sjlongland/dcdcconv-sensor-pcb/gerber/sensor-In2.Cu.pdf

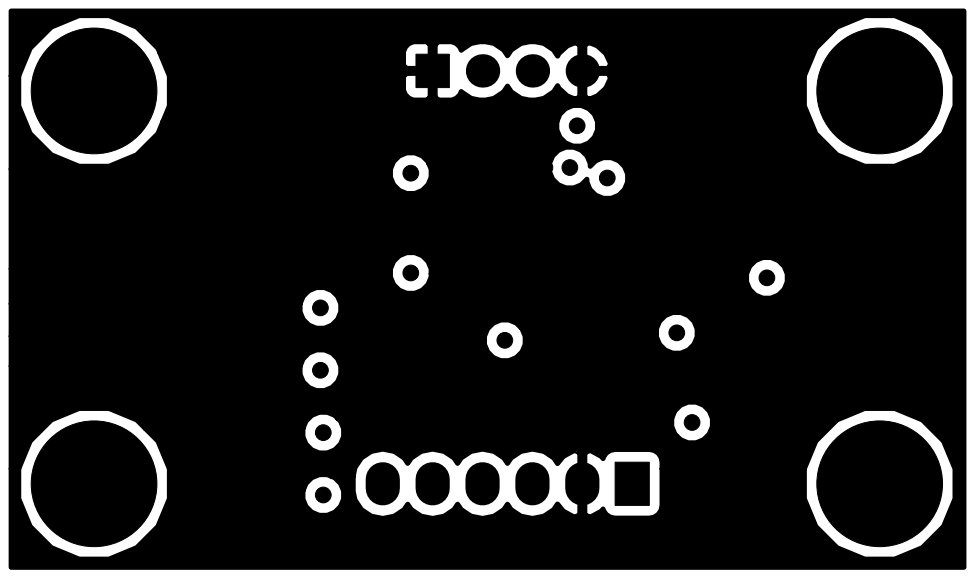
[picture p12: page 1]
